mfrisch3/ece315_project/drivers/ece315.h

#ifndef __ECE315_H__
#define __ECE315_H__

#include "cyhal.h"
#include "cy_pdl.h"
#include "cybsp.h"
#include <stdint.h>
#include <stdbool.h>
#include <stdlib.h>


#include "ece315_buttons.h"
#include "ece315_buzzer.h"
#include "ece315_leds.h"
#include "timer.h"

#endif
